soupie-62/Keypad/Board_V1a.jpg

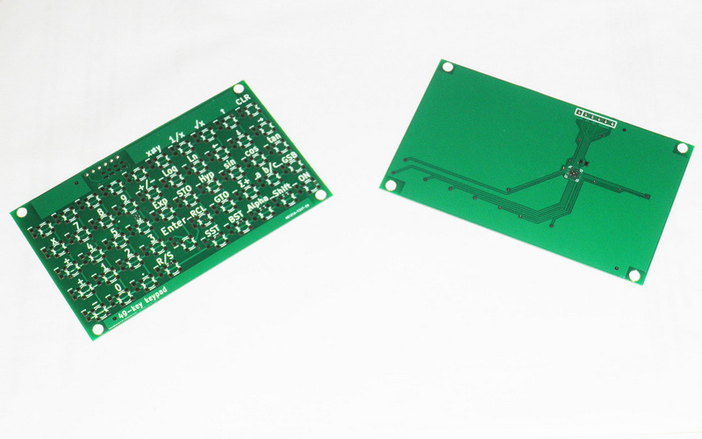
Board_V1a.jpg
