soupie-62/Keypad/docs/PDF/Keys/hp41_keys.PNG

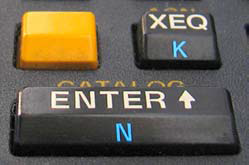
docs/PDF/Keys/hp41_keys.PNG
