soupie-62/Keypad/docs/PDF/Keys/Switches_2014_0312.pdf

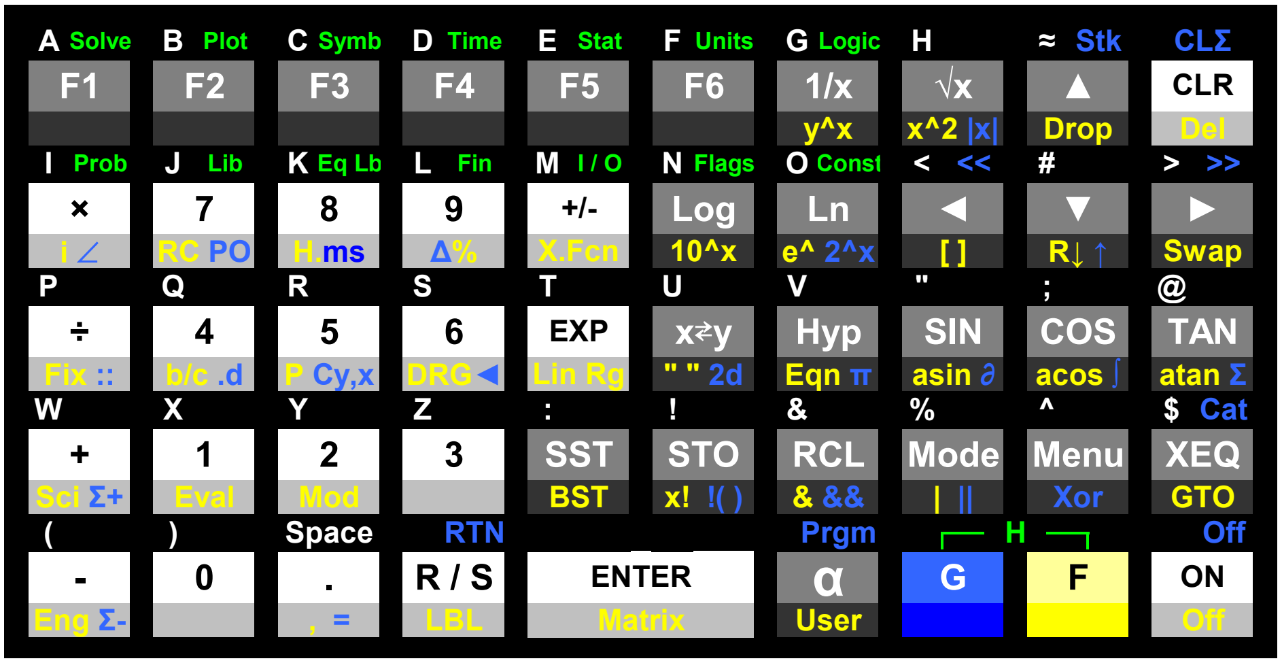
[picture p4: figure]
D Time; Stat; Prgm; Const; A Solve; Plot; C Symb; F Units; Fix ::; Sci Σ+; Eval; Space; RTN; EXP; STO; Mode; Hyp; Eqn π; Prob; X.Fcn; Flags; asin ∂; SIN; TAN; Cat; COS; Logic; Eng Σ-; CLΣ; Stk; Del >; LBL; User; Swap; RCL; Log; atan Σ; acos ∫; Menu; Off; Xor; GTO; XEQ; Mod; Drop; CLR; DRG◄; Lin Rg; Lib; Fin; ENTER; Matrix; SST; BST
