soupie-62/Keypad/docs/Connect_1.PNG

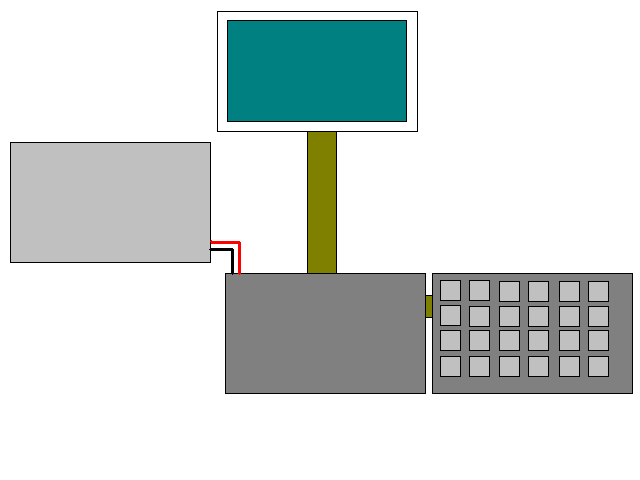
docs/Connect_1.PNG
