soupie-62/Keypad/docs/Connect_2.PNG

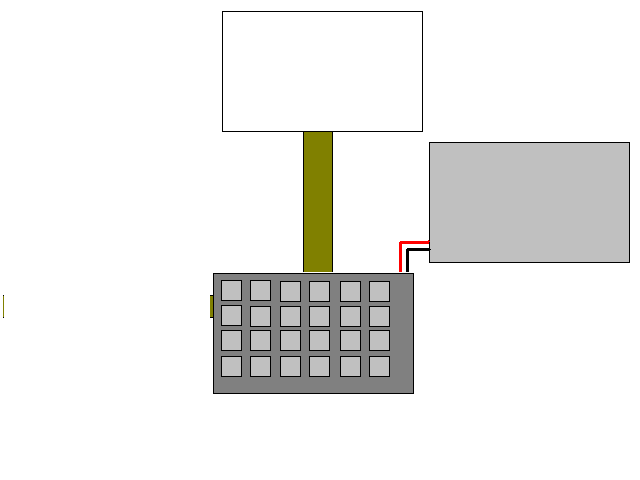
docs/Connect_2.PNG
