soupie-62/Keypad/docs/Connect_3.PNG

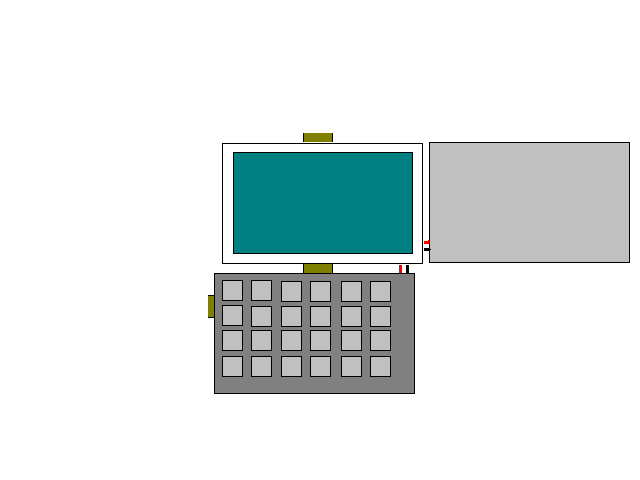
docs/Connect_3.PNG
