soupie-62/Keypad/docs/Connect_4.PNG

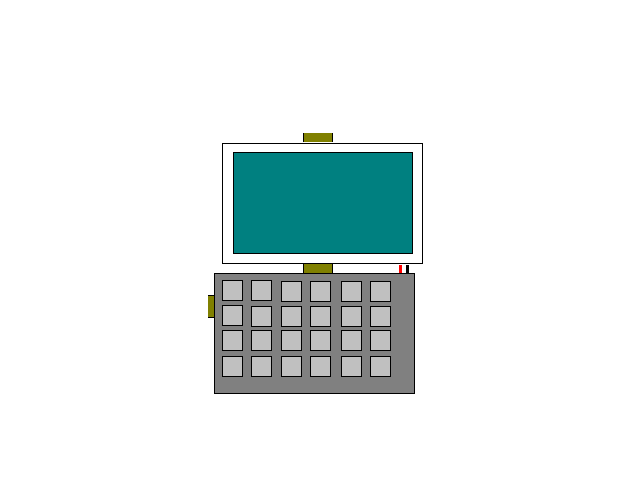
docs/Connect_4.PNG
