soupie-62/Keypad/docs/Connect_5.png

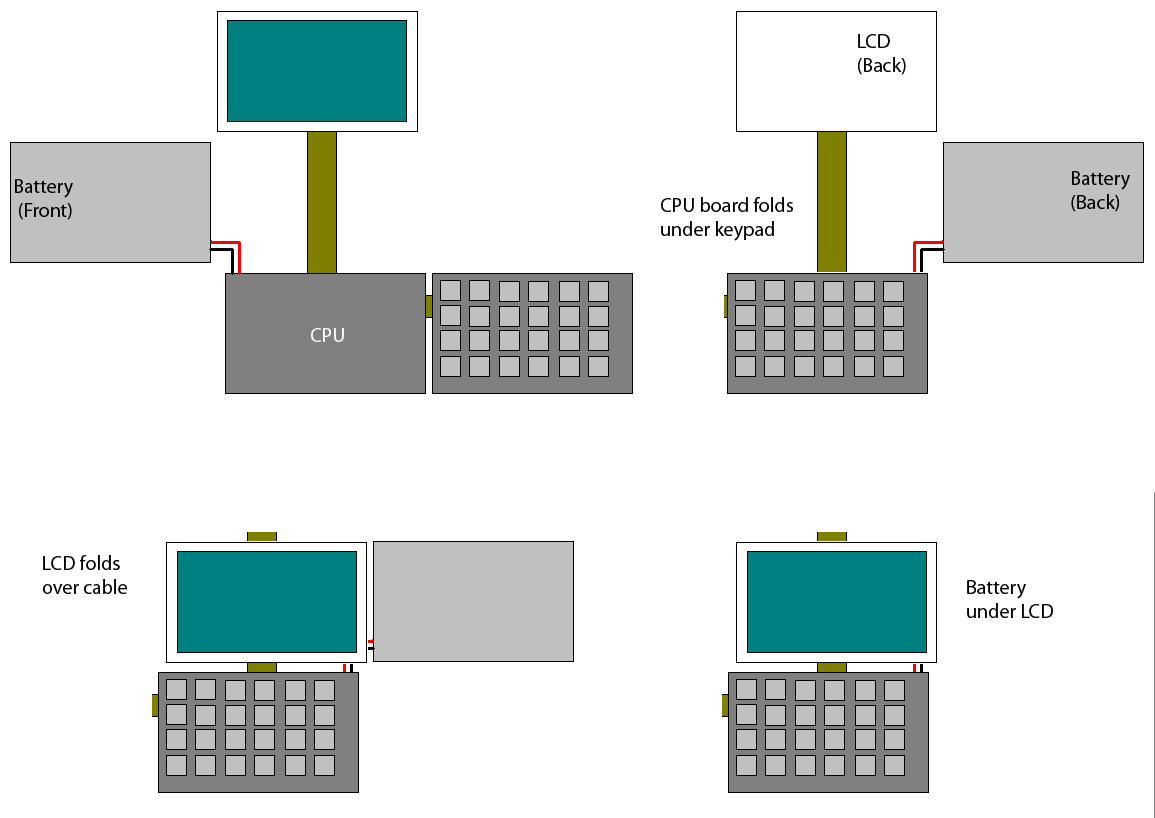
docs/Connect_5.png
