soupie-62/Keypad/docs/PDF/Keys/4Pin 7mm x 5mm SKQGAFE010 - Alps.gif

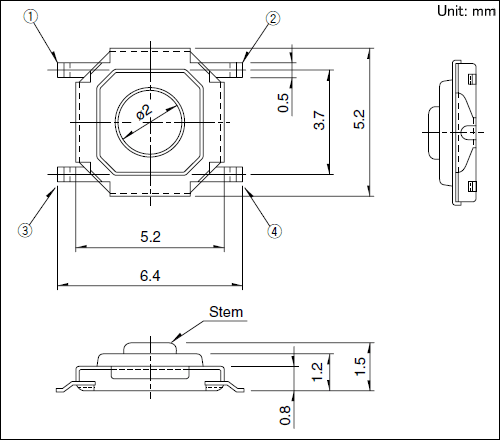
docs/PDF/Keys/4Pin 7mm x 5mm SKQGAFE010 - Alps.gif
