soupie-62/Keypad/docs/www/Nexus_7/_4_B_00.png

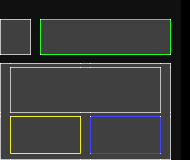
docs/www/Nexus_7/_4_B_00.png
