soupie-62/Keypad/docs/www/Nexus_7/alpha/A_Layout.png

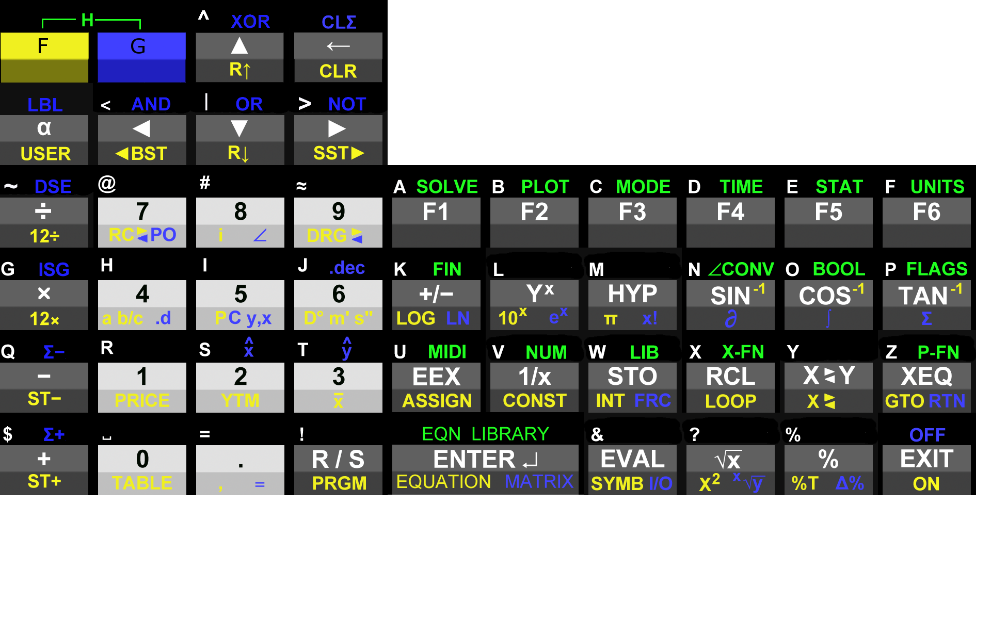
docs/www/Nexus_7/alpha/A_Layout.png
