soupie-62/Keypad/docs/www/Nexus_7/alpha/A_R0C1.png

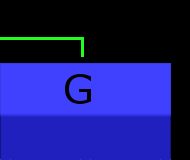
docs/www/Nexus_7/alpha/A_R0C1.png
