soupie-62/Keypad/docs/www/Nexus_7/alpha/A_R2C6.png

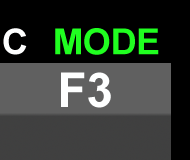
docs/www/Nexus_7/alpha/A_R2C6.png
