soupie-62/Keypad/docs/www/Nexus_7/alpha/A_R3C0.png

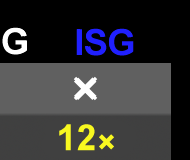
docs/www/Nexus_7/alpha/A_R3C0.png
