soupie-62/Keypad/docs/www/Nexus_7/alpha/A_R3C3.png

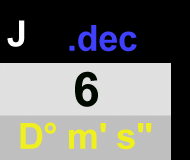
docs/www/Nexus_7/alpha/A_R3C3.png
