soupie-62/Keypad/docs/www/Nexus_7/alpha/A_R4C0.png

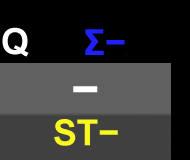
docs/www/Nexus_7/alpha/A_R4C0.png
