soupie-62/Keypad/docs/www/Nexus_7/alpha/A_R4C5.png

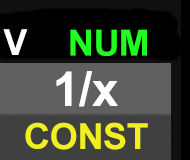
docs/www/Nexus_7/alpha/A_R4C5.png
