soupie-62/Keypad/docs/www/Nexus_7/alpha/A_R4C8.png

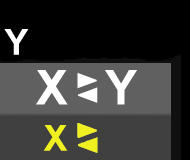
docs/www/Nexus_7/alpha/A_R4C8.png
