soupie-62/Keypad/docs/www/Nexus_7/B_R0C0_F.png

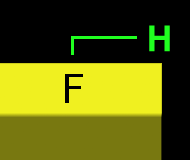
docs/www/Nexus_7/B_R0C0_F.png
