soupie-62/Keypad/docs/www/Nexus_7/B_R5C4_ENTER.png

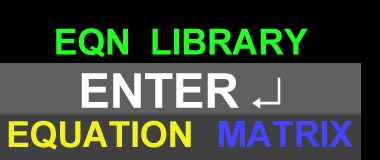
docs/www/Nexus_7/B_R5C4_ENTER.png
