soupie-62/Keypad/docs/www/Nexus_7/F/F_Layout.png

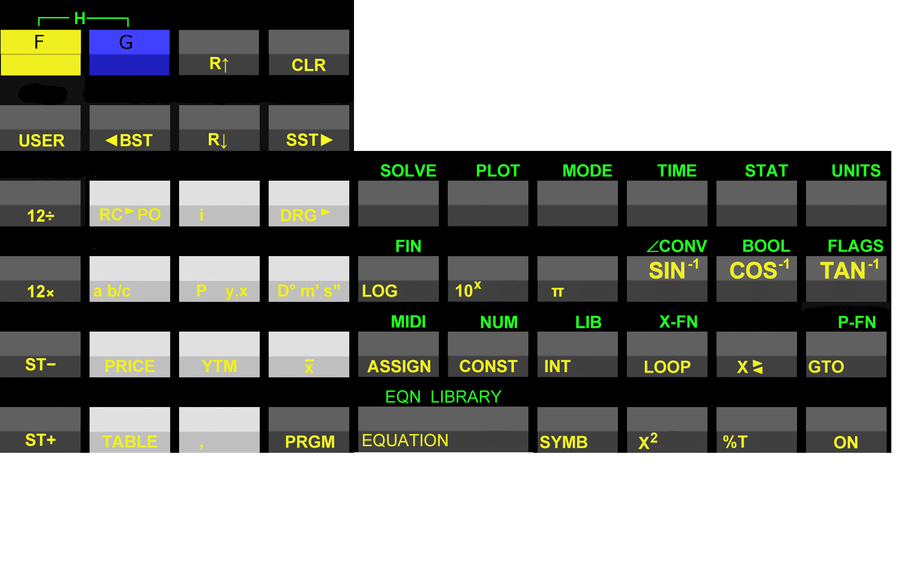
docs/www/Nexus_7/F/F_Layout.png
