soupie-62/Keypad/docs/www/Nexus_7/F/F_R0C2.png

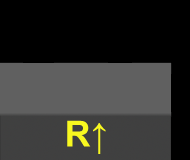
docs/www/Nexus_7/F/F_R0C2.png
