soupie-62/Keypad/docs/www/Nexus_7/F/F_R2C5.png

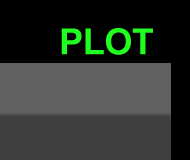
docs/www/Nexus_7/F/F_R2C5.png
