soupie-62/Keypad/docs/www/Nexus_7/F/F_R3C6.png

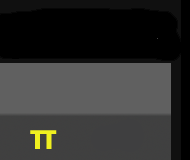
docs/www/Nexus_7/F/F_R3C6.png
