soupie-62/Keypad/docs/www/Nexus_7/F/F_R4C3.png

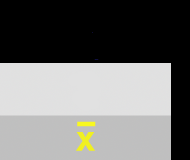
docs/www/Nexus_7/F/F_R4C3.png
