soupie-62/Keypad/docs/www/Nexus_7/F/F_R5C4.png

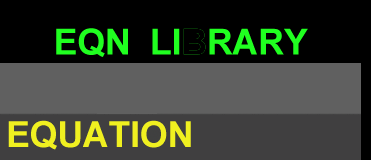
docs/www/Nexus_7/F/F_R5C4.png
