soupie-62/Keypad/docs/www/Nexus_7/H/H_Layout.png

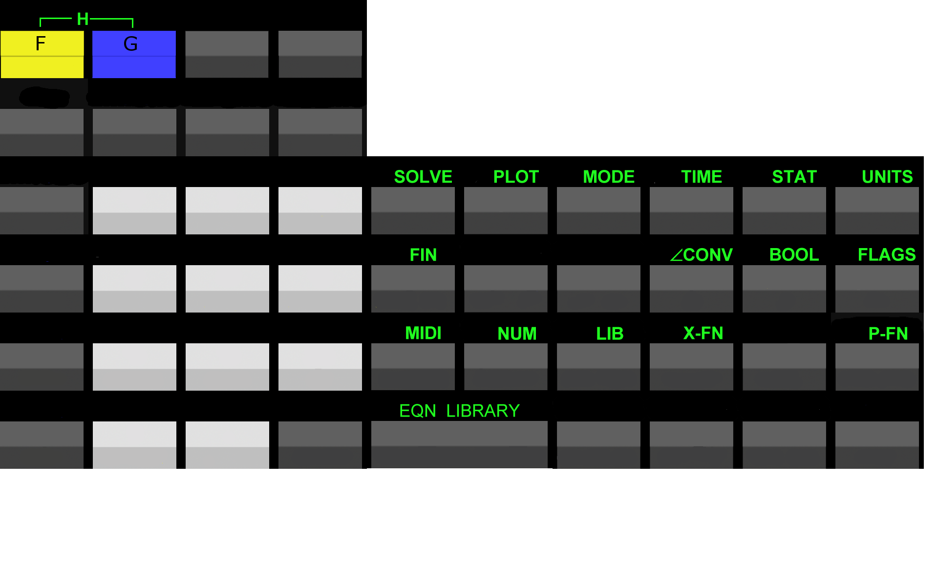
docs/www/Nexus_7/H/H_Layout.png
