soupie-62/Keypad/docs/www/Nexus_7/H/H_R0C3.png

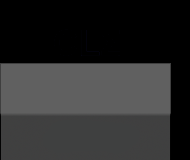
docs/www/Nexus_7/H/H_R0C3.png
