soupie-62/Keypad/docs/www/Nexus_7/H/H_R3C0.png

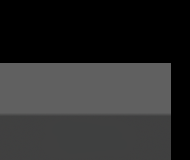
docs/www/Nexus_7/H/H_R3C0.png
