soupie-62/Keypad/docs/www/Nexus_7/H/H_R4C5.png

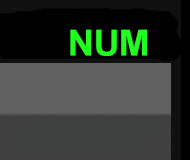
docs/www/Nexus_7/H/H_R4C5.png
