soupie-62/Keypad/docs/www/Sample/css/themes/shinyredbutton.png

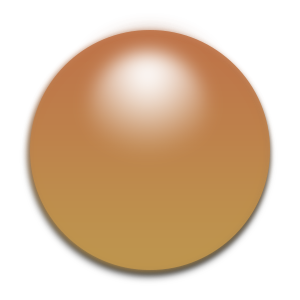
docs/www/Sample/css/themes/shinyredbutton.png
