soupie-62/Keypad/docs/PDF/Keys/PmodKYPD_sch.pdf

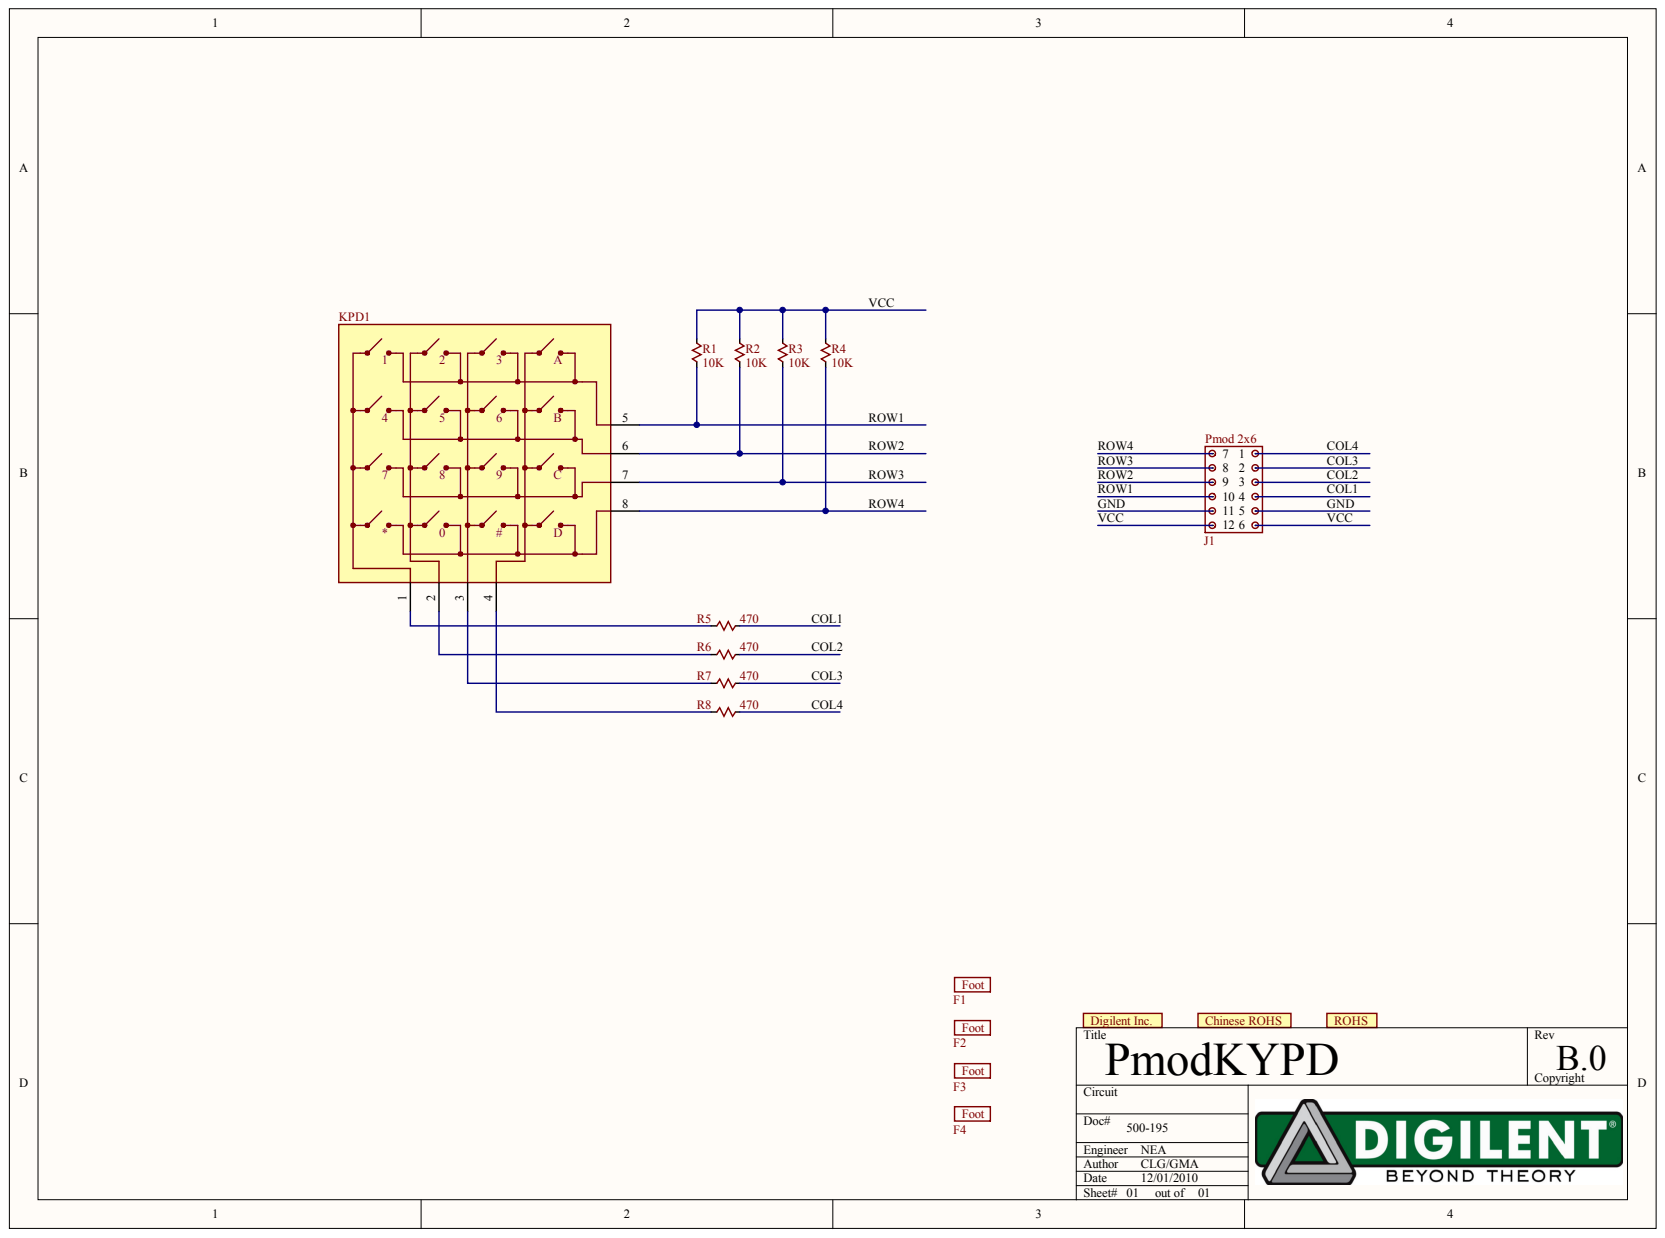
[picture p97: page 1]

7 | ROW3

8 | ROW4

Title PmodKYPD | Rev B.0 Copyright

Circuit
