soupie-62/Keypad/docs/PDF/Connectors/Pin Header x1.pdf

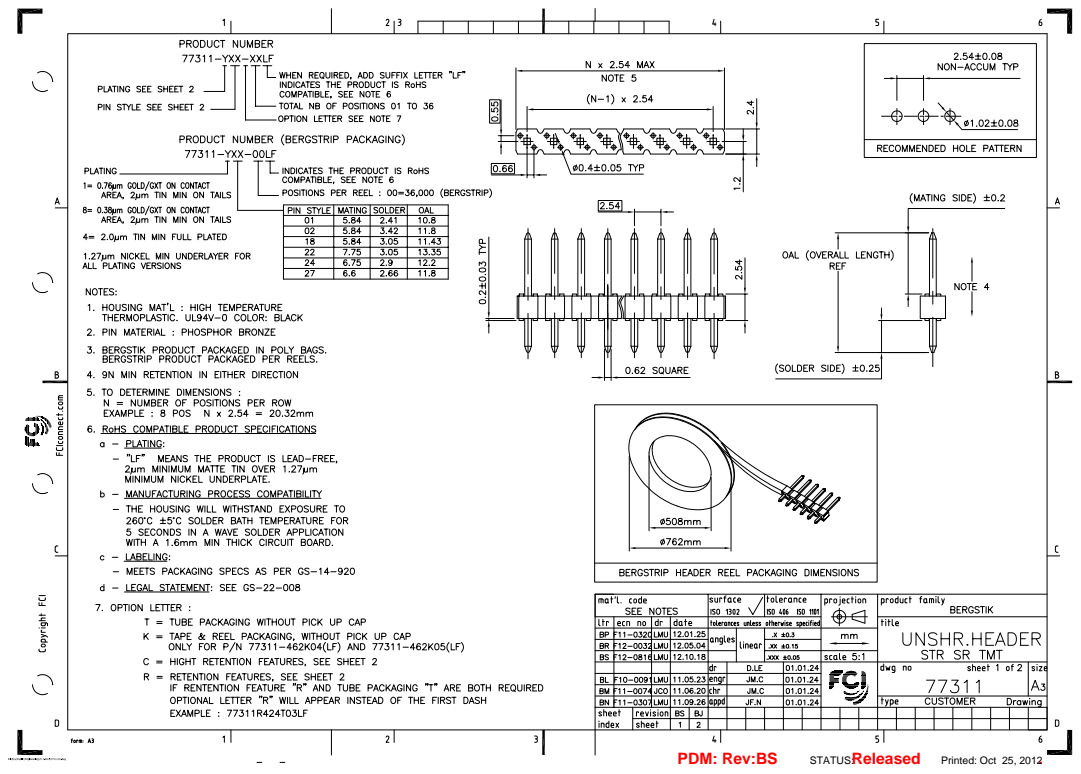
[picture p98: page 1]
PDM: Rev:BS; Released; . STATUS:; Printed: Oct 25, 2012

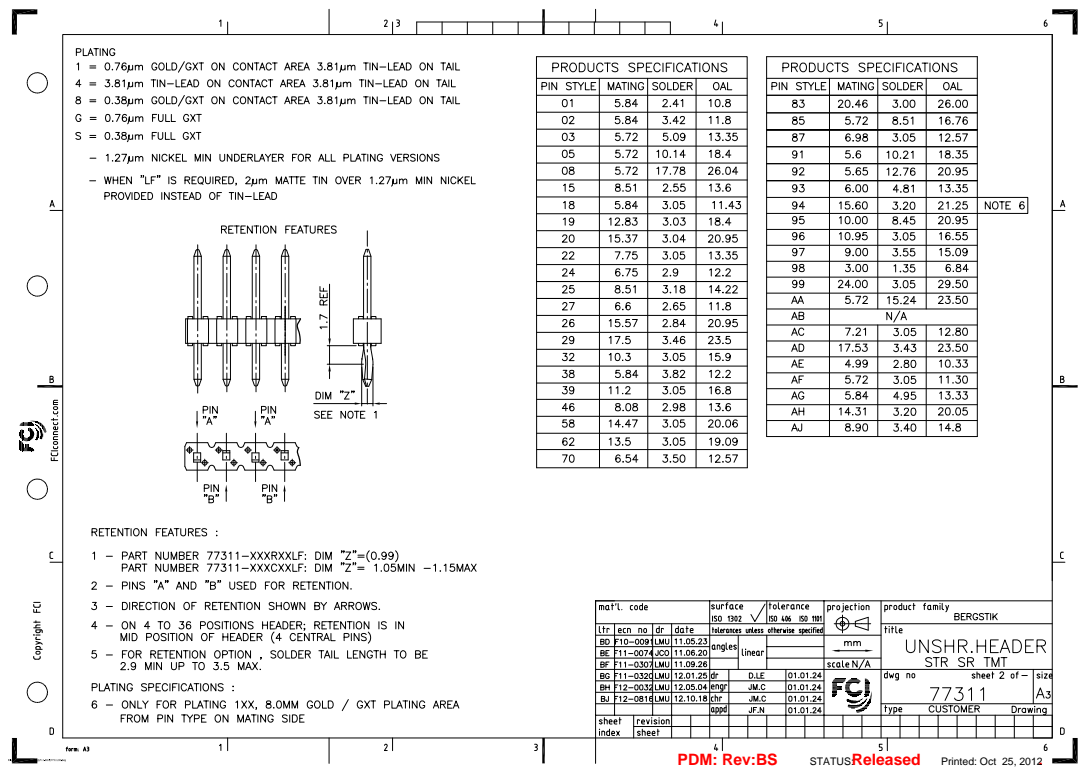
[picture p99: page 2]
PDM: Rev:BS; Released; . STATUS:; Printed: Oct 25, 2012
