soupie-62/Keypad/docs/PDF/Key Encoder/ADP5589 - PmodIOXP_sch.pdf

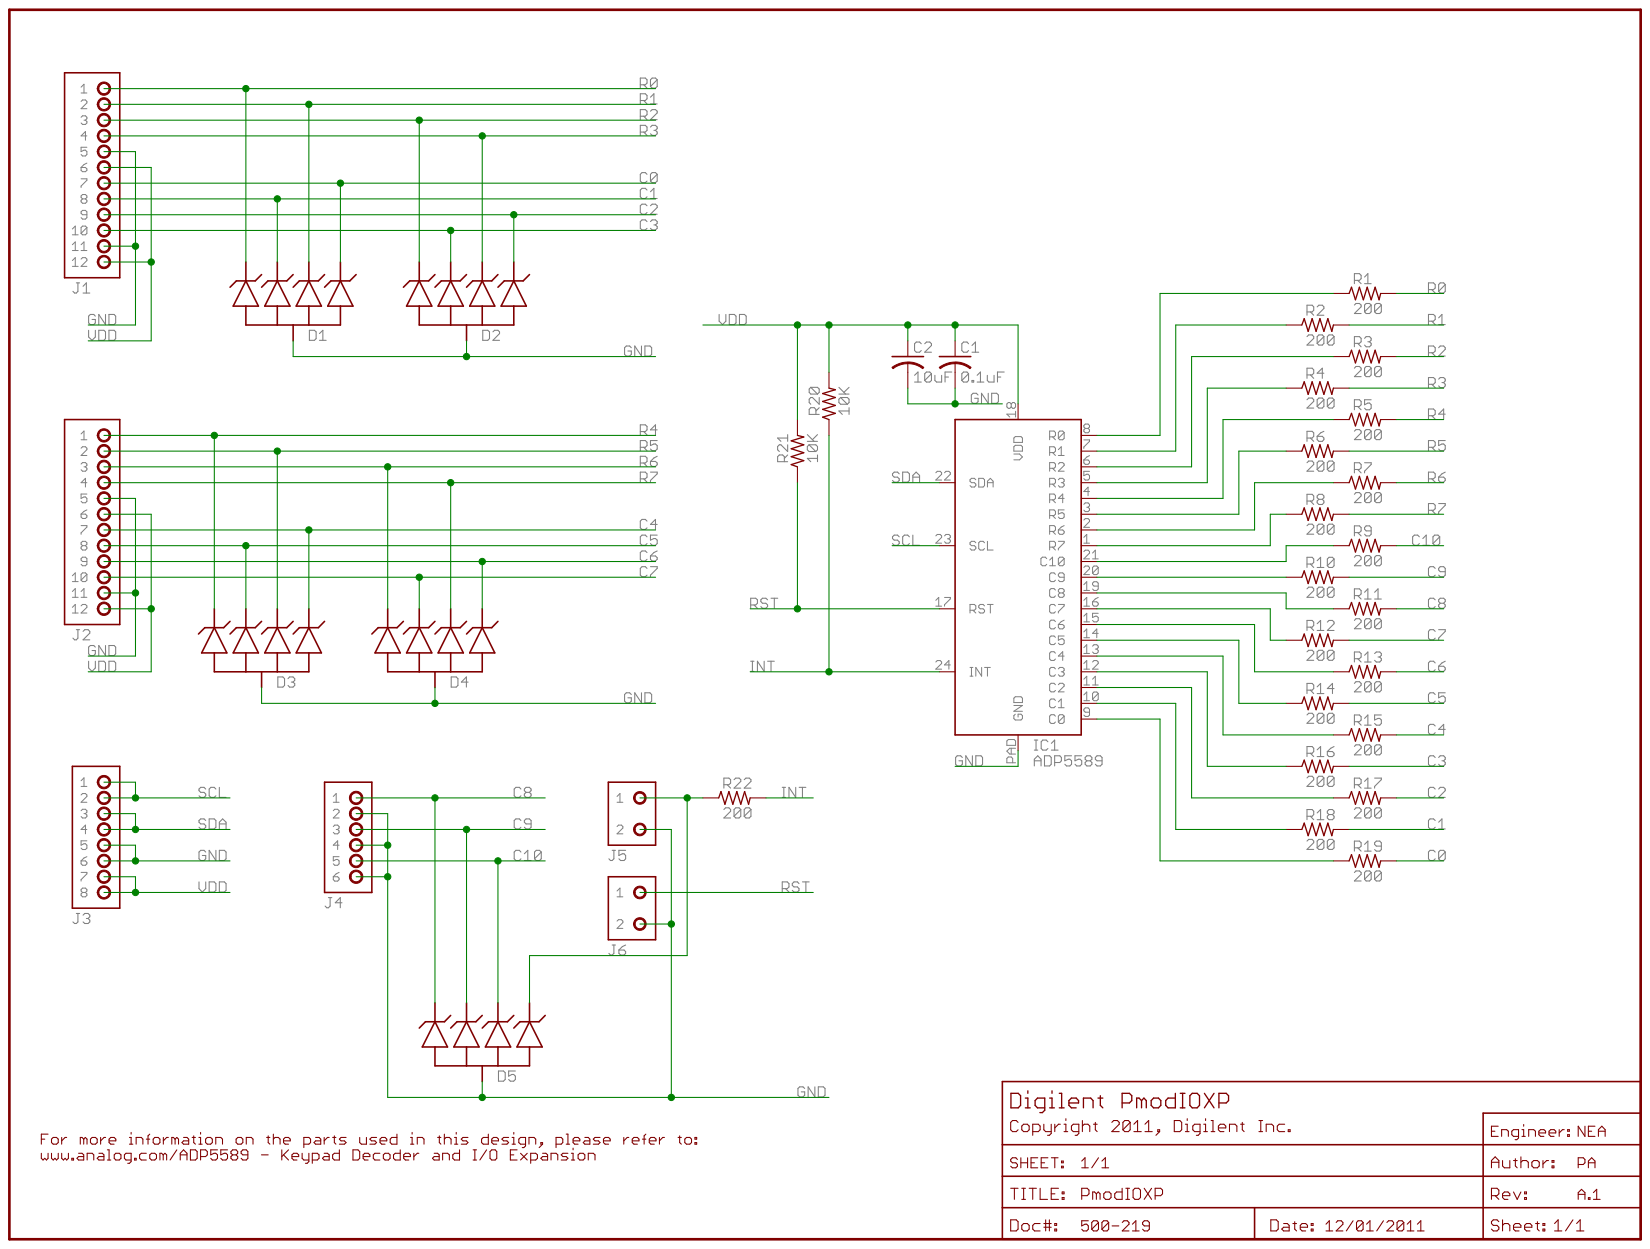
[picture p102: page 1]
