soupie-62/Keypad/docs/PDF/Power/SparkFun LiPo Charger - PowerCell-v13.pdf

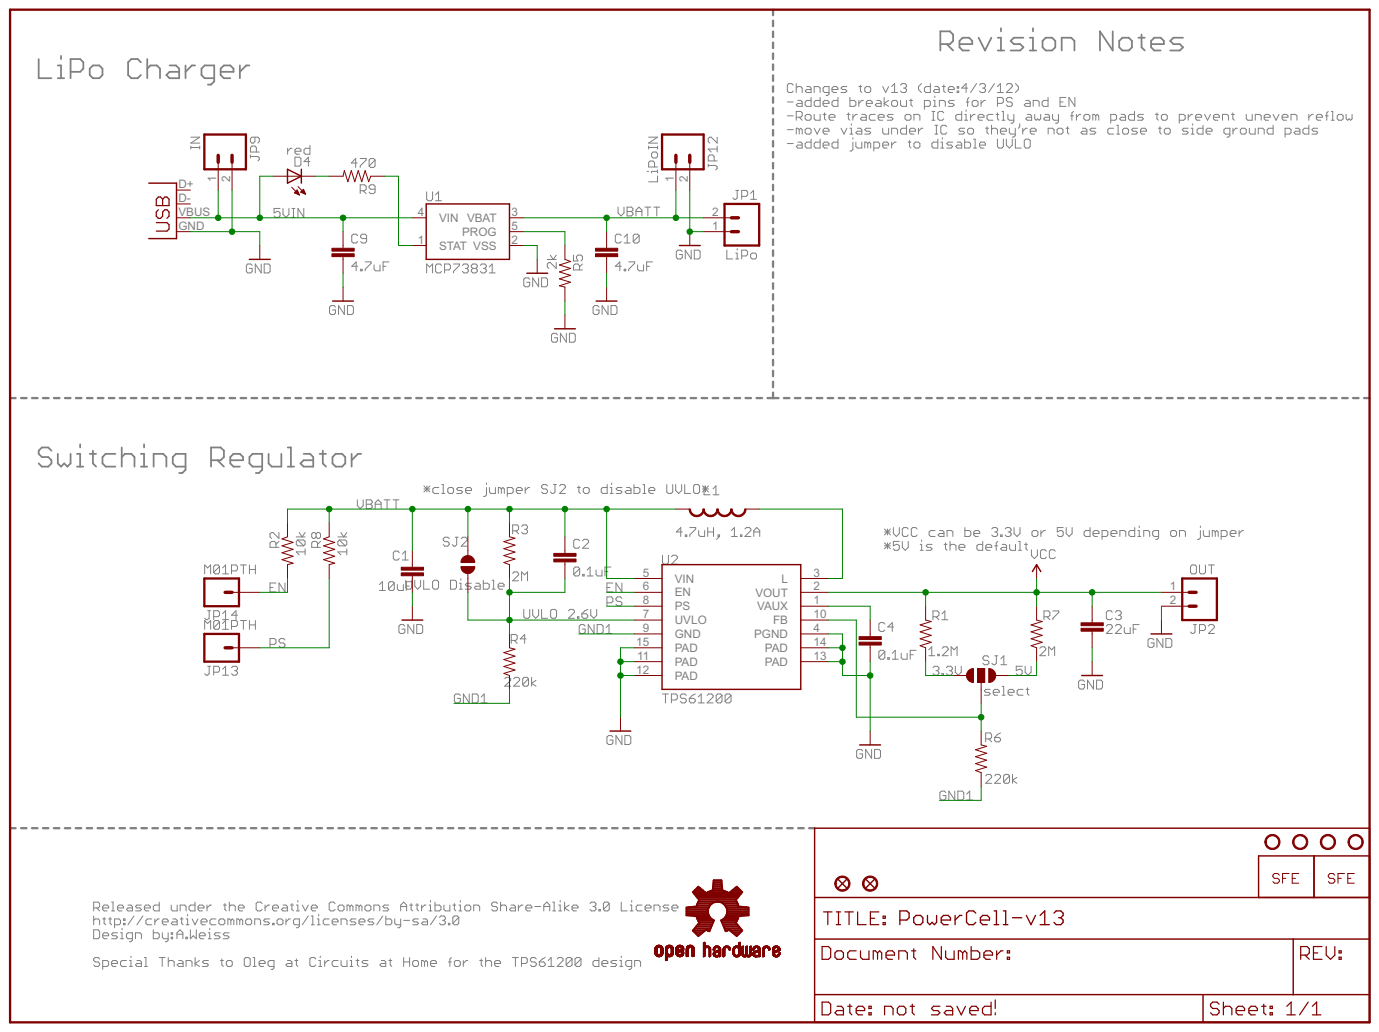
[picture p103: page 1]
